kaini/lcdclock/firmware/dcf77_parser.cpp

#include "dcf77_parser.hpp"
#include "utils.hpp"
#include <algorithm>

static dcf77::bit parse_bit(const bool* samples, size_t start_index) {
    // Count the time low in the first 200 ms.
    int low_ms = 0;
    for (size_t i = 0; i < dcf77::samples_per_second / 5; ++i) {
        size_t index = i + start_index;
        if (index >= dcf77::samples_per_second) {
            index -= dcf77::samples_per_second;
        }
        if (!samples[index]) {
            low_ms += 1000 / dcf77::samples_per_second;
        }
    }

    if (low_ms <= 20) {
        return dcf77::bit::minute_mark;
    } else if (60 <= low_ms && low_ms <= 120) {
        return dcf77::bit::zero;
    } else if (180 <= low_ms) {
        return dcf77::bit::one;
    } else {
        return dcf77::bit::unknown;
    }
}

template <typename Container>
static dcf77::bit ripple_add(Container& bits, dcf77::bit carry) {
    using dcf77::bit;
    static constexpr bit add_result_table[4][4] = {
        /*                       bit::unknown, bit::zero,    bit::one,     bit::minute_mark */
        /* bit::unknown */     { bit::unknown, bit::unknown, bit::unknown, bit::unknown },
        /* bit::zero */        { bit::unknown, bit::zero,    bit::one,     bit::unknown },
        /* bit::one */         { bit::unknown, bit::one,     bit::zero,    bit::unknown },
        /* bit::minute_mark */ { bit::unknown, bit::unknown, bit::unknown, bit::unknown },
    };
    static constexpr bit add_carry_table[4][4] = {
        /*                       bit::unknown, bit::zero,    bit::one,     bit::minute_mark */
        /* bit::unknown */     { bit::unknown, bit::zero,    bit::unknown, bit::unknown },
        /* bit::zero */        { bit::zero,    bit::zero,    bit::zero,    bit::zero    },
        /* bit::one */         { bit::unknown, bit::zero,    bit::one,     bit::unknown },
        /* bit::minute_mark */ { bit::unknown, bit::zero,    bit::unknown, bit::unknown },
    };

    for (size_t i = 0; i < bits.size(); ++i) {
        bit value = bits[i];
        bits[i] = add_result_table[static_cast<size_t>(value)][static_cast<size_t>(carry)];
        carry = add_carry_table[static_cast<size_t>(value)][static_cast<size_t>(carry)];
    }
    return carry;
}

template <typename Container>
static bool is_parity_valid(const Container& bits, dcf77::bit parity) {
    using dcf77::bit;

    if (parity == bit::unknown || parity == bit::minute_mark) {
        return false;
    } else {
        bool result = false;
        for (size_t i = 0; i < bits.size(); ++i) {
            if (bits[i] == bit::zero) {
                // no-op
            } else if (bits[i] == bit::one) {
                result = !result;
            } else {
                return false;
            }
        }
        return result ? (parity == bit::one) : (parity == bit::zero);
    }
}

template <typename Container>
static int parse_valid_number(const Container& bits) {
    int result = 0;
    for (size_t i = 0; i < bits.size(); ++i) {
        result += (1 << i) * (bits[i] == dcf77::bit::one);
    }
    return result;
}

dcf77::bit_sync::bit_sync() {
    std::fill(m_histogram.begin(), m_histogram.end(), 0);
}

void dcf77::bit_sync::feed(const bool samples[samples_per_second]) {
    for (size_t i = 0; i < samples_per_second; ++i) {
        m_histogram[i] += samples[i];
    }
    m_count += 1;

    if (m_count >= 10) {
        // Find the 100 ms band with the lowest values. The beginning of this
        // band is the second start. The applied kernel is therefore
        // [>1<; 1; 1; 1; 1; 1; 1; 1; 1; 1]
        int current_value =
            m_histogram[0] +
            m_histogram[1] +
            m_histogram[2] +
            m_histogram[3] +
            m_histogram[4] +
            m_histogram[5] +
            m_histogram[6] +
            m_histogram[7] +
            m_histogram[8] +
            m_histogram[9];
        int min_value = current_value;
        size_t min_index = 0;
        for (size_t i = 1; i < samples_per_second; ++i) {
            // Subtract the old leftmost value.
            current_value -= m_histogram[i - 1];

            // Add the new rightmost value
            size_t right_index = i + 9;
            if (right_index >= samples_per_second) {
                right_index -= samples_per_second;
            }
            current_value += m_histogram[right_index];

            if (current_value < min_value) {
                min_value = current_value;
                min_index = i;
            }
        }

        std::fill(m_histogram.begin(), m_histogram.end(), 0);
        m_count = 0;
        m_bit_start = min_index;
    }
}

dcf77::frame_sync::frame_sync() {
    std::fill(m_histogram.begin(), m_histogram.end(), 0);
}

void dcf77::frame_sync::feed(bit bit) {
    if (bit == bit::minute_mark) {
        m_histogram[m_at] += 1;

        // The counters have to be clamped every now and then to avoid that it takes
        // a too long time to resync the minute mark if it changes after a leap
        // second or other errors.
        if (m_histogram[m_at] > 3) {
            std::fill(m_histogram.begin(), m_histogram.end(), 0);
            m_histogram[m_at] = 1;
        }

        // Set a new minute mark if this is new new maximum.
        if (m_at != m_frame_start && m_histogram[m_at] > m_histogram[m_frame_start]) {
            m_frame_start = m_at;
        }
    }

    m_at += 1;
    if (m_at >= bits_per_minute) {
        m_at = 0;
    }
}

dcf77::parser::parser() {
    std::fill(m_new_bits.begin(), m_new_bits.end(), bit::unknown);
    std::fill(m_result.bits.begin(), m_result.bits.end(), bit::unknown);
}

bool dcf77::parser::feed(const bool* samples) {
    m_bit_sync.feed(samples);
    if (m_bit_sync.bit_start() == size_t(-1)) {
        return false;
    }

    bit bit = parse_bit(samples, m_bit_sync.bit_start());
    m_frame_sync.feed(bit);
    m_new_bits[m_at] = bit;

    bool result = false;
    if (m_at == m_frame_sync.frame_start()) {
        consume_dataframe();
        result = true;
    }

    m_at += 1;
    if (m_at >= bits_per_minute) {
        m_at = 0;
    }

    return result;
}

void dcf77::parser::consume_dataframe() {
    // First simulate an increment on the existing minute
    bit carry = ripple_add(m_result.minute_ones, bit::one);
    int minimum_value = 16 * (carry == bit::one) +
                         8 * (m_result.minute_ones[3] == bit::one) +
                         4 * (m_result.minute_ones[2] == bit::one) +
                         2 * (m_result.minute_ones[1] == bit::one) +
                         1 * (m_result.minute_ones[0] == bit::one);
    int maximum_value = 16 * (carry != bit::zero) +
                         8 * (m_result.minute_ones[3] != bit::zero) +
                         4 * (m_result.minute_ones[2] != bit::zero) +
                         2 * (m_result.minute_ones[1] != bit::zero) +
                         1 * (m_result.minute_ones[0] != bit::zero);
    ASSERT(0 <= minimum_value && minimum_value <= maximum_value);

    if (maximum_value < 10) {
        // If the value is beween 0 and 9 the tens do not need to be increased.
    } else if (minimum_value == 10 && maximum_value == 10) {
        // If the value is 10 the tens need to be incremented and the ones need
        // to be reset.
        m_result.minute_ones[0] = bit::zero;
        m_result.minute_ones[1] = bit::zero;
        m_result.minute_ones[2] = bit::zero;
        m_result.minute_ones[3] = bit::zero;
        ripple_add(m_result.minute_tens, bit::one);
    } else if (minimum_value > 10) {
        // Something is wrong if the minimum value is greater than 10.
        // The field is out of range. Forget everything we know about the ones
        // and possibly increment the tens.
        m_result.minute_ones[0] = bit::unknown;
        m_result.minute_ones[1] = bit::unknown;
        m_result.minute_ones[2] = bit::unknown;
        m_result.minute_ones[3] = bit::unknown;
        ripple_add(m_result.minute_tens, bit::unknown);
    } else if (maximum_value >= 10) {
        // It might be required to flip the tens if the maximum might be bigger or
        // equal to 10.
        ripple_add(m_result.minute_tens, bit::unknown);
    }

    // Recalculate the parity. If one bit is unkown the whole parity is unkown.
    m_result.minute_parity = bit::zero;
    for (size_t i = 0; i < m_result.minute_bits.size(); ++i) {
        if (m_result.minute_bits[i] == bit::zero) {
            // no-op
        } else if (m_result.minute_bits[i] == bit::one) {
            // xor
            if (m_result.minute_parity == bit::zero) {
                m_result.minute_parity = bit::one;
            } else {
                m_result.minute_parity = bit::zero;
            }
        } else {
            // unknown
            m_result.minute_parity = bit::unknown;
            break;
        }
    }

    static constexpr bit combine_table[4][4] = {
        /*                       bit::unknown,     bit::zero,    bit::one,     bit::minute_mark */
        /* bit::unknown */     { bit::unknown,     bit::zero,    bit::one,     bit::unknown },
        /* bit::zero */        { bit::zero,        bit::zero,    bit::unknown, bit::zero    },
        /* bit::one */         { bit::one,         bit::unknown, bit::one,     bit::one     },
        /* bit::minute_mark */ { bit::unknown,     bit::zero,    bit::one,     bit::unknown },
    };
    for (size_t i = 0; i < bits_per_minute - 1; ++i) {
        size_t source_i = i + m_frame_sync.frame_start() + 1;
        if (source_i >= bits_per_minute) {
            source_i -= bits_per_minute;
        }
        m_result.bits[i] = combine_table[static_cast<size_t>(m_result.bits[i])][static_cast<size_t>(m_new_bits[source_i])];
    }

    // This value is hardcoded here, because its position is decided by handle_minute_mark.
    m_result.bits.back() = bit::minute_mark;
}

std::experimental::optional<datetime::datetime> dcf77::parser::get_result() const {
	bool layout_valid =
	    m_result.zero == bit::zero &&
	    m_result.one == bit::one &&
	    m_result.minute_mark == bit::minute_mark &&
        (
            (m_result.in_dst == bit::one && m_result.not_in_dst == bit::zero) ||
            (m_result.in_dst == bit::zero && m_result.not_in_dst == bit::one)
        );
	if (!layout_valid) {
	    DEBUG_PRINTF("Invalid DCF frame layout\n");
		return {};
	}

    if (!is_parity_valid(m_result.minute_bits, m_result.minute_parity)) {
        DEBUG_PRINTF("Invalid DCF minute parity\n");
    	return {};
    }
    int minute = parse_valid_number(m_result.minute_ones) + parse_valid_number(m_result.minute_tens) * 10;

    if (!is_parity_valid(m_result.hour_bits, m_result.hour_parity)) {
        DEBUG_PRINTF("Invalid DCF hour parity\n");
    	return {};
    }
    int hour = parse_valid_number(m_result.hour_ones) + parse_valid_number(m_result.hour_tens) * 10;

    if (!is_parity_valid(m_result.date_bits, m_result.date_parity)) {
        DEBUG_PRINTF("Invalid DCF date parity\n");
        return {};
    }
    int day = parse_valid_number(m_result.day_ones) + parse_valid_number(m_result.day_tens) * 10;
    int month = parse_valid_number(m_result.month_ones) + parse_valid_number(m_result.month_tens) * 10;
    int year = 2000 + parse_valid_number(m_result.year_ones) + parse_valid_number(m_result.year_tens) * 10;

    bool isdst = m_result.in_dst == bit::one;

    try {
        datetime::datetime result(year, month, day, hour, minute, 0);
        if (isdst) {
            result.add_hours(-2);
        } else {
            result.add_hours(-1);
        }
        return result;
    } catch (const datetime::invalid_datetime_exception&) {
        DEBUG_PRINTF("Invalid DCF datetime received\n");
        return {};
    }
}
